SFB-ELAINE/STELLA/STELLA RF SHIELD/Firmware/Raspberry Pi/cc2500_val.py

class value():
    
    def __init__(self):
        None

    VAL_IOCFG2           = 0x29
    VAL_IOCFG1           = 0x2E
    VAL_IOCFG0           = 0x06
    VAL_FIFOTHR          = 0x07
    VAL_SYNC1            = 0xD3
    VAL_SYNC0            = 0x91
    VAL_PKTLEN           = 0xFF
    VAL_PKTCTRL1         = 0x04  # 04
    VAL_PKTCTRL0         = 0x05
    VAL_ADDR             = 0x00   # 00
    VAL_CHANNR           = 0x01
    VAL_FSCTRL1          = 0x0A   #0x08
    VAL_FSCTRL0          = 0x00
    VAL_FREQ2            = 0x5D   # 5D
    VAL_FREQ1            = 0x94   # 93
    VAL_FREQ0            = 0x48   # B1
    VAL_MDMCFG4          = 0x2D   #0x8D   # 86
    VAL_MDMCFG3          = 0x3B   # 83
    VAL_MDMCFG2          = 0x73   #0x73   # 03
    VAL_MDMCFG1          = 0x23   #0x22
    VAL_MDMCFG0          = 0x3B   #0xF8
    VAL_DEVIATN          = 0x01   #0x44
    VAL_MCSM2            = 0x07  #07 ,02
    VAL_MCSM1            = 0x30
    VAL_MCSM0            = 0x18
    VAL_FOCCFG           = 0x1D   #0x16
    VAL_BSCFG            = 0x1C   #0x6C
    VAL_AGCCTRL2         = 0xC7   #0x03
    VAL_AGCCTRL1         = 0x00   #0x40
    VAL_AGCCTRL0         = 0xB0   #0x91
    VAL_WOREVT1          = 0x87
    VAL_WOREVT0          = 0x6B
    VAL_WORCTRL          = 0xF8
    VAL_FREND1           = 0xB6   #0x56
    VAL_FREND0           = 0x10
    VAL_FSCAL3           = 0xEA   #0xA9
    VAL_FSCAL2           = 0x0A
    VAL_FSCAL1           = 0x00
    VAL_FSCAL0           = 0x11
    VAL_RCCTRL1          = 0x41
    VAL_RCCTRL0          = 0x00
    VAL_FSTEST           = 0x59
    VAL_PTEST            = 0x7F
    VAL_AGCTEST          = 0x3F
    VAL_TEST2            = 0x88
    VAL_TEST1            = 0x31
    VAL_TEST0            = 0x0B
    VAL_PARTNUM          = 0x80
    VAL_VERSION          = 0x03
    VAL_FREQEST          = 0x00
    VAL_LQI              = 0x00
    VAL_RSSI             = 0x00
    VAL_MARCSTATE        = 0x00
    VAL_WORTIME1         = 0x00
    VAL_WORTIME0         = 0x00
    VAL_PKTSTATUS        = 0x00
    VAL_VCO_VC_DAC       = 0x00
    VAL_TXBYTES          = 0x00
    VAL_RXBYTES          = 0x00
    VAL_RCCTRL1_STATUS   = 0x00
    VAL_RCCTRL0_STATUS   = 0x00
