SFB-ELAINE/STELLA/STELLA RF SHIELD/Firmware/STELLA/BlinkPattern.h

#ifndef BLINKPATTERN_H_
#define BLINKPATTERN_H_


void ImpedanceBlinkPattern(Impedance_Status impedanceStatus, Stimulation_Channel channel);
void LowBatteryPattern(void);
void LowImpedancePattern(void);
void HighImpedancePattern(void);
void EverythingIsFinePattern(void);
void StimulationOffPattern(void);
void ErrorDetectionPattern(void);
void StartErrorRecognitionPattern(void);
void PacketNotReceive(void);
void ContinuousTxnPattern(void);

#endif
